TheSonicZone/ThermalPrinterPOC/test_graphics_384_384.bmp

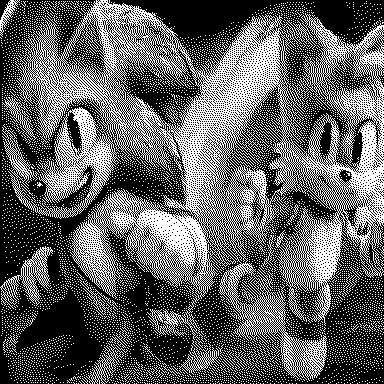
test_graphics_384_384.bmp
